laroo/Marstek-ModBus-Gateway/src/config.h

#pragma once

// Stringify helper macros
#define STRINGIFY(x) #x
#define TOSTRING(x) STRINGIFY(x)

// OTA credentials (passed as bare identifiers via -D flags, stringified here)
#ifndef OTA_USERNAME
#error Need to define OTA_USERNAME
#endif
#ifndef OTA_PASSWORD
#error Need to define OTA_PASSWORD
#endif
#define OTA_USERNAME_STR TOSTRING(OTA_USERNAME)
#define OTA_PASSWORD_STR TOSTRING(OTA_PASSWORD)

// MQTT broker
#ifndef MQTT_BROKER
#define MQTT_BROKER "test.mosquitto.org"
#endif
#ifndef MQTT_PORT
#define MQTT_PORT 1883
#endif


#ifndef MQTT_USERNAME
#define MQTT_USERNAME nullptr
#endif
#ifndef MQTT_PASSWORD
#define MQTT_PASSWORD nullptr
#endif

// MQTT topic prefix
#ifndef MQTT_TOPIC_STATUS
#define MQTT_TOPIC_STATUS "marstek-modbus-gateway/status"
#endif
#ifndef MQTT_TOPIC_COMMAND
#define MQTT_TOPIC_COMMAND "marstek-modbus-gateway/command"
#endif
